clutxh11/CapstoneGroup52/controlCode/testScript/data/encoder.png

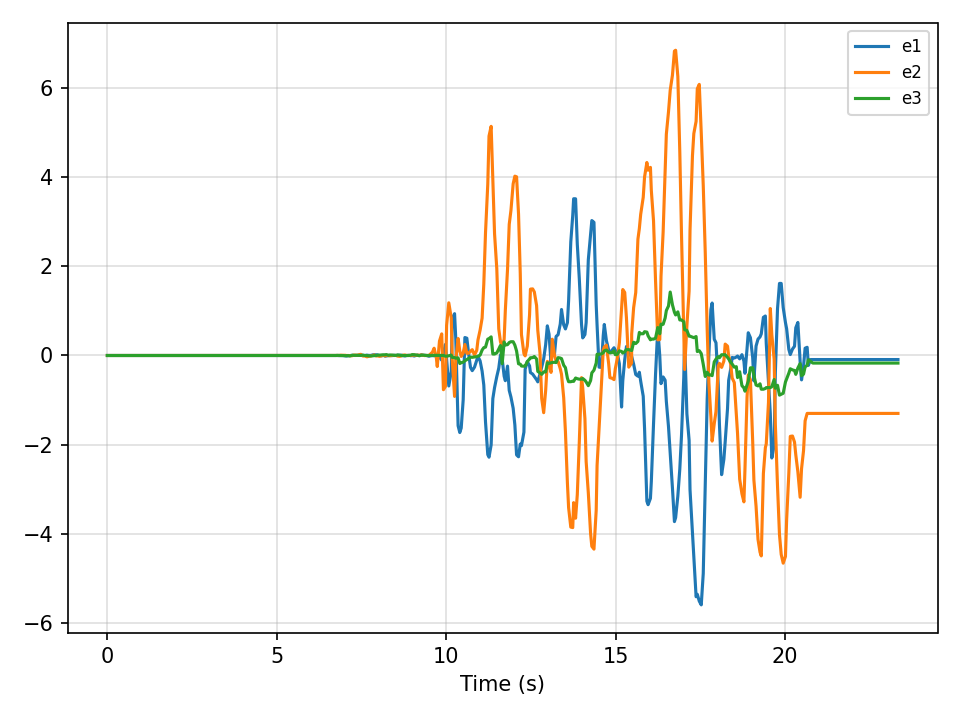
controlCode/testScript/data/encoder.png
