clutxh11/CapstoneGroup52/controlCode/testScript/data/vel_commands.png

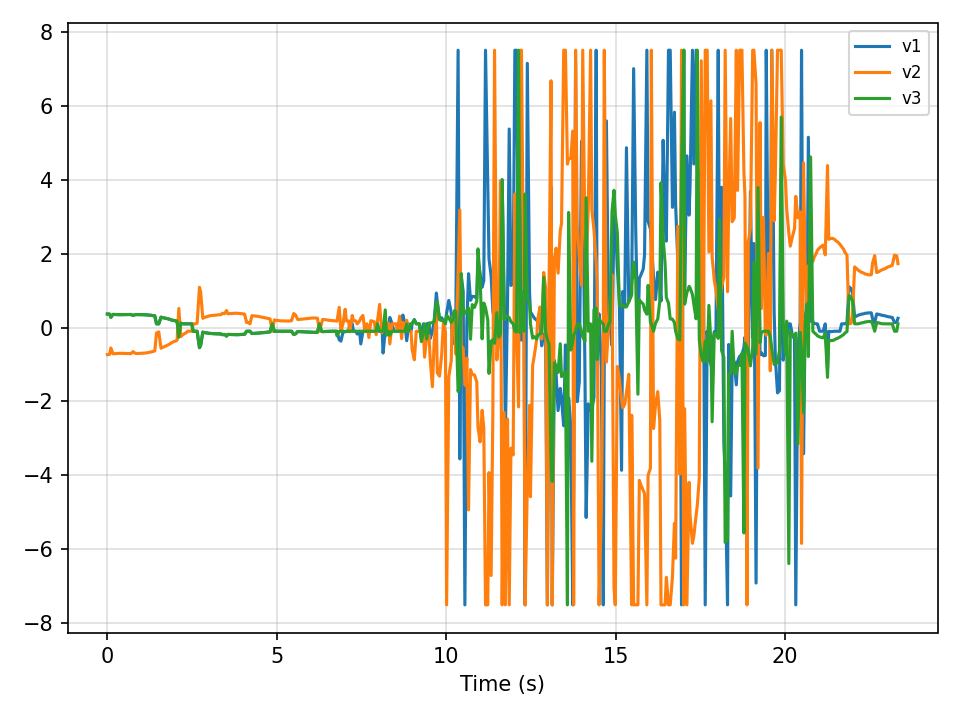
controlCode/testScript/data/vel_commands.png
